jackha/pixel-clock/arduino/pixel-clock/bitmap.h

#define BITMAP_TM 0
#define BITMAP_LO 8
#define BITMAP_GM 16
#define BITMAP_OK 24
#define BITMAP_NO 32
#define BITMAP_PACMAN0 40
#define BITMAP_PACMAN1 48
#define BITMAP_GHOST0 56
#define BITMAP_GHOST1 64

#define BITMAP_ROBOT_BASE1 72
#define BITMAP_ROBOT_BASE2 80
#define BITMAP_ROBOT_BASE3 88
#define BITMAP_ROBOT_EYES1 96
#define BITMAP_ROBOT_EYES2 104
#define BITMAP_ROBOT_ARMS1 112
#define BITMAP_ROBOT_ARMS2 120
#define BITMAP_ROBOT_ARMS3 128
#define BITMAP_ROBOT_LEGS1 136
#define BITMAP_ROBOT_LEGS2 144

static const unsigned char bitmaps[] PROGMEM = {
  // 'set' aka 'time'
  0b00000000,
  0b11011010,
  0b10010011,
  0b11011010,
  0b01010010,
  0b11011001,
  0b00000000,
  0b00000000,

  // lo layout
  0b11111000,
  0b10001000,
  0b10001111,
  0b10001001,
  0b10001001,
  0b11111001,
  0b00010001,
  0b00011111,

  // game
  0b01000110,
  0b10001001,
  0b10101111,
  0b11101001,
  0b00000000,
  0b11110011,
  0b10101010,
  0b10101001,

  // ok
  0b00000000,
  0b01001001,
  0b10101010,
  0b10101100,
  0b10101110,
  0b10101001,
  0b01001001,
  0b00000000,

  // no
  0b00000000,
  0b10010010,
  0b11010101,
  0b10110101,
  0b10010101,
  0b10010010,
  0b00000000,
  0b00000000,

  // pac man frame 0
  0b00111100,
  0b01111110,
  0b11111111,
  0b11111111,
  0b11111111,
  0b11111111,
  0b01111110,
  0b00111100,

  // pac man frame 1
  0b00111100,
  0b01111110,
  0b00011111,
  0b00001111,
  0b00001111,
  0b00011111,
  0b01111110,
  0b00111100,

  // ghost frame 0
  0b00111110,
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
  0x00, 0x00, 0x00,  0x40, 0x00, 0x00,  0x40, 0x00, 0x00,  0x00, 0x00, 0x00,  0x00, 0x00, 0x00,  0x00, 0x00, 0x20,  0x00, 0x00, 0x00,  0x00, 0x00, 0x20,  
};
